marsherino/flatbox-bugfromstreetsremix/hardware-rev5/images/20230830_204837.jpg

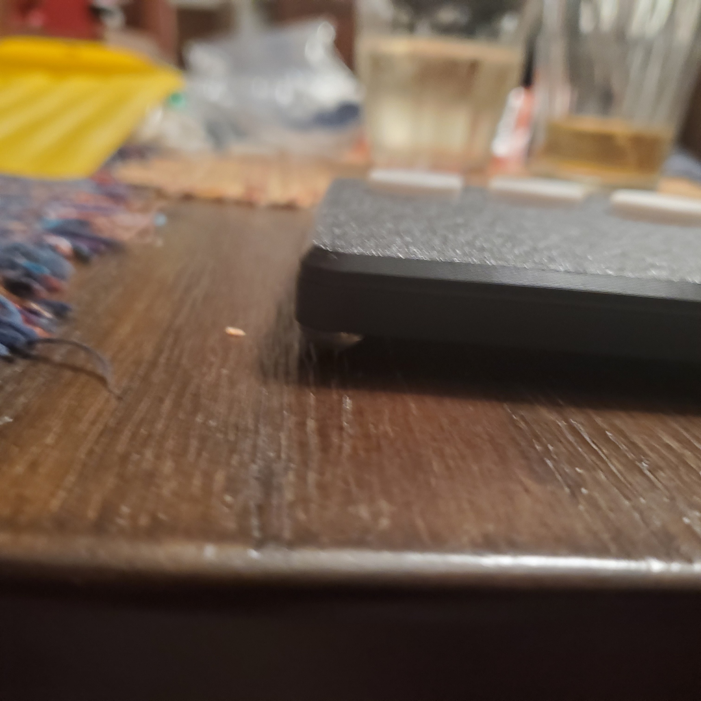
hardware-rev5/images/20230830_204837.jpg
